ZiyiWang58/talking-plant-radio/hardware/images/01.jpg

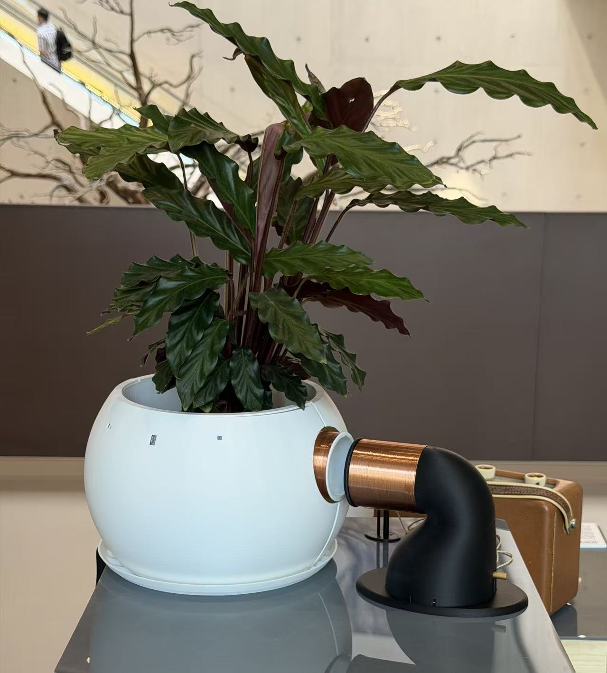
hardware/images/01.jpg
