ZiyiWang58/talking-plant-radio/hardware/images/02.jpg

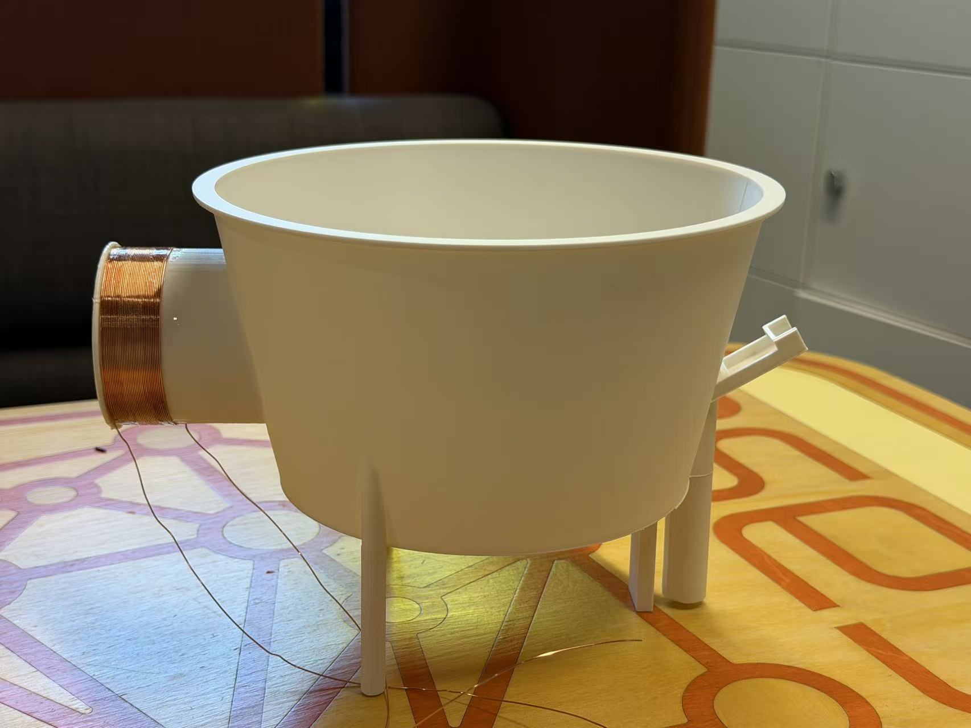
hardware/images/02.jpg
