ZiyiWang58/talking-plant-radio/hardware/images/03.jpg

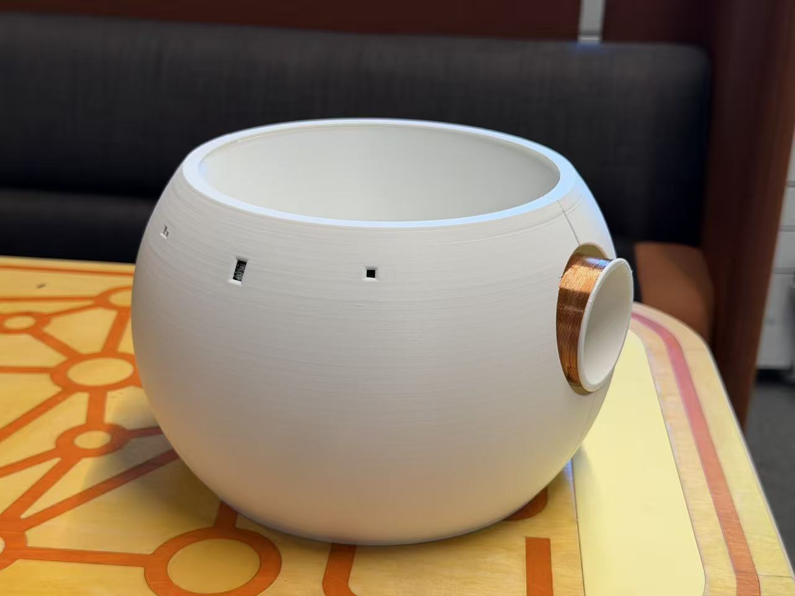
hardware/images/03.jpg
