ZiyiWang58/talking-plant-radio/hardware/images/04.jpg

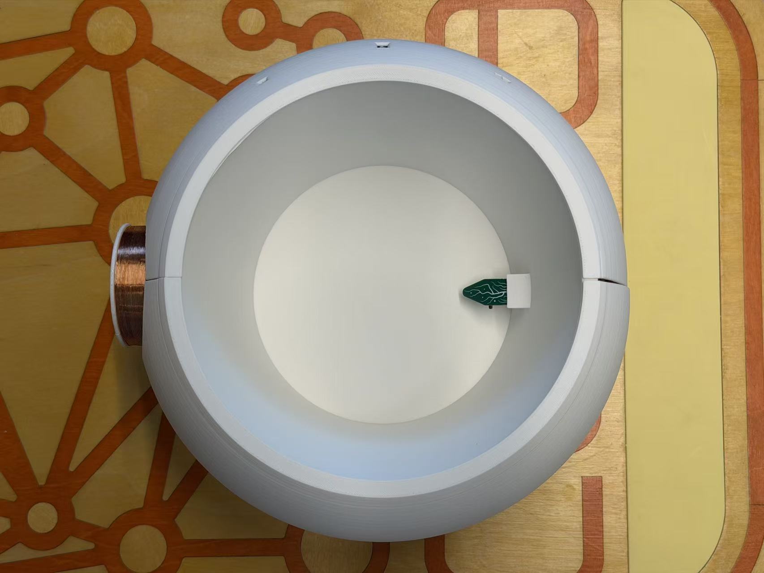
hardware/images/04.jpg
