ZiyiWang58/talking-plant-radio/hardware/images/figure2.jpg

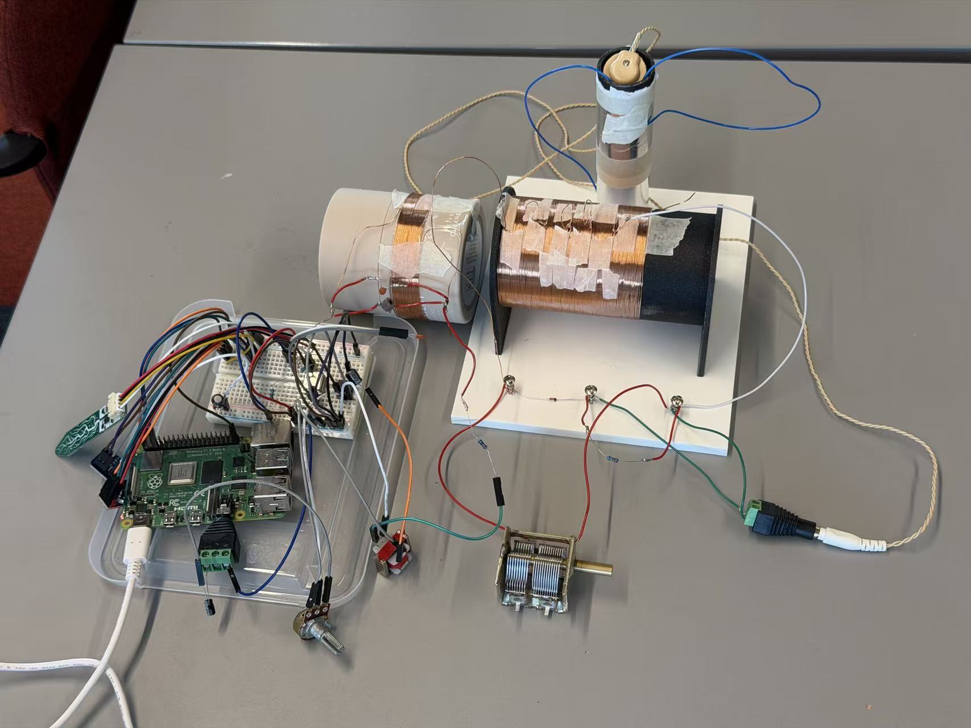
hardware/images/figure2.jpg
