ZiyiWang58/talking-plant-radio/hardware/images/PCB1.jpg

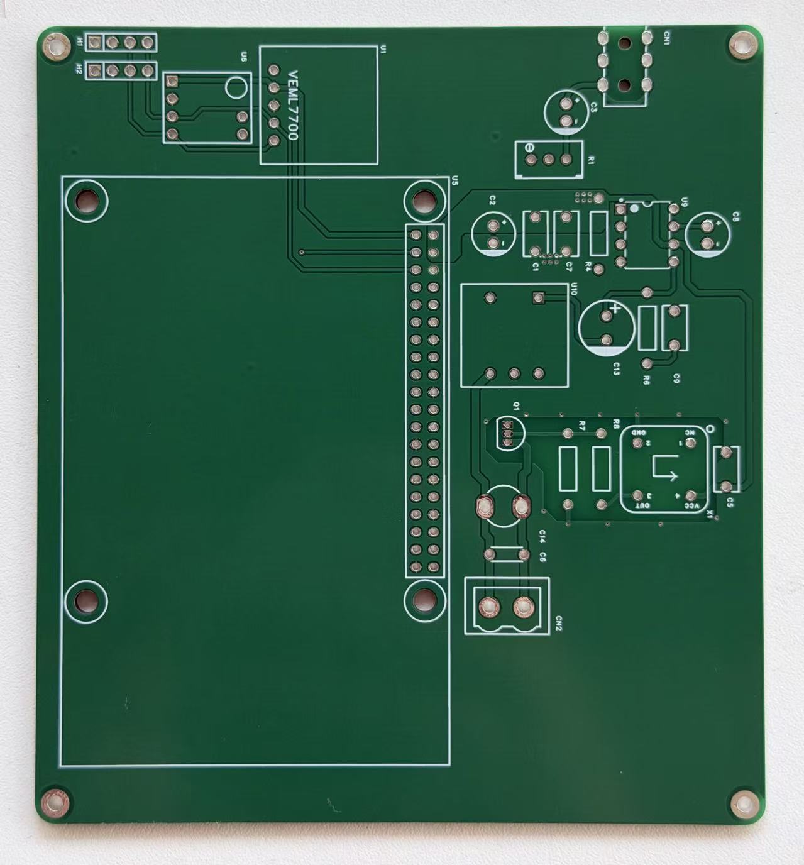
hardware/images/PCB1.jpg
