ZiyiWang58/talking-plant-radio/hardware/images/PCB2.jpg

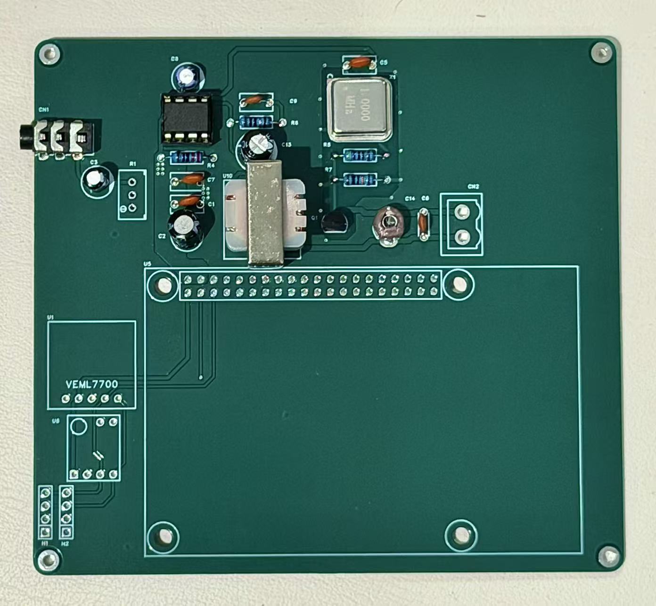
hardware/images/PCB2.jpg
