ZiyiWang58/talking-plant-radio/hardware/images/radio1.png

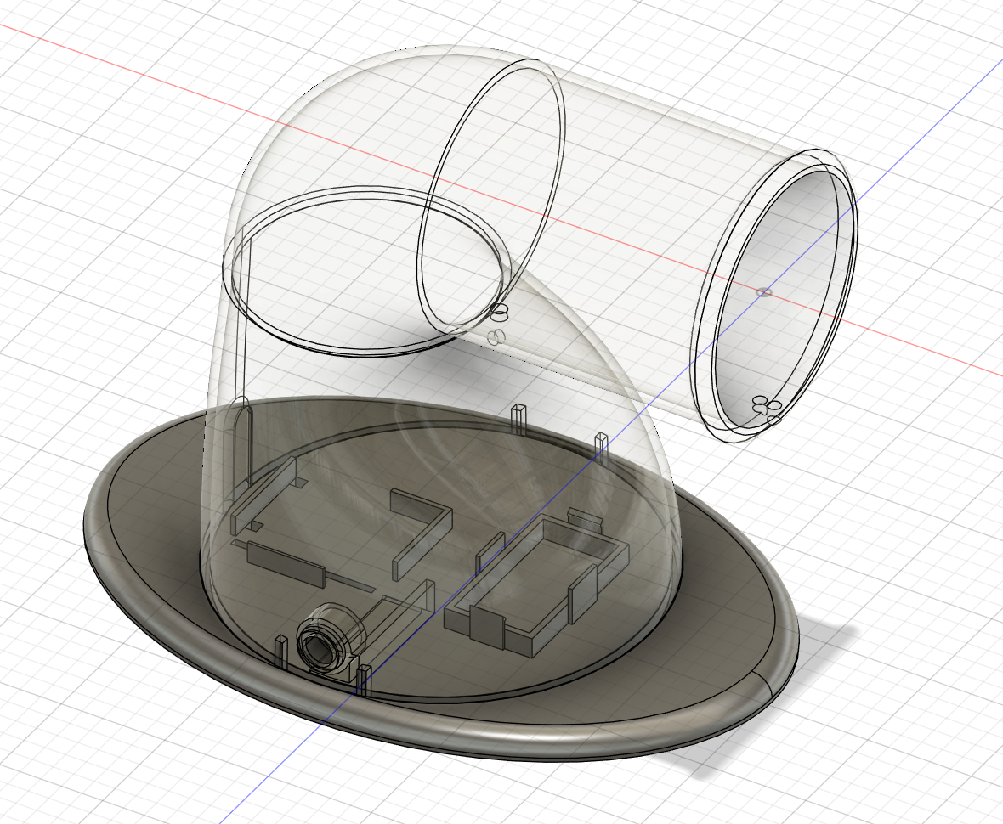
hardware/images/radio1.png
