ZiyiWang58/talking-plant-radio/hardware/images/radio2.jpg

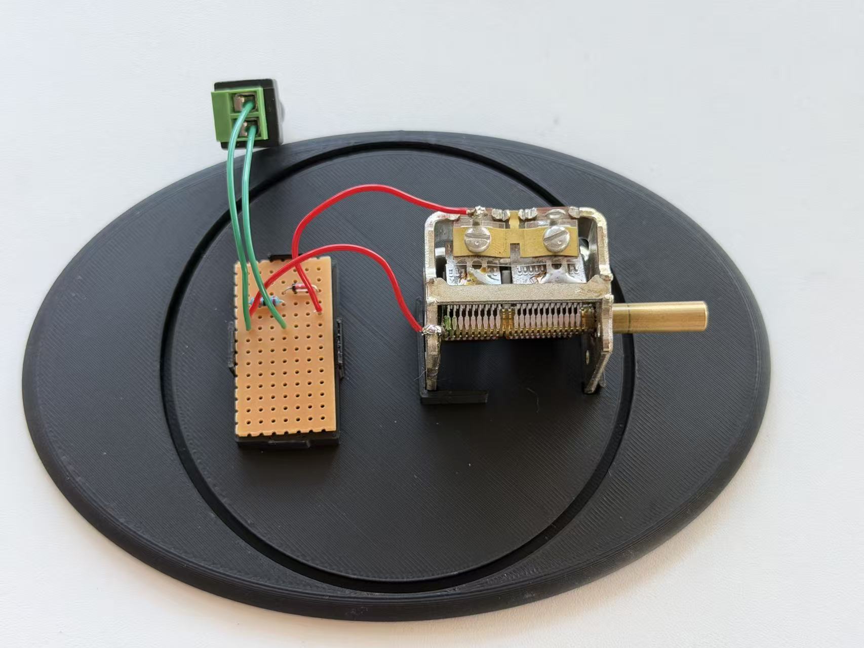
hardware/images/radio2.jpg
