ZiyiWang58/talking-plant-radio/hardware/images/radio.png

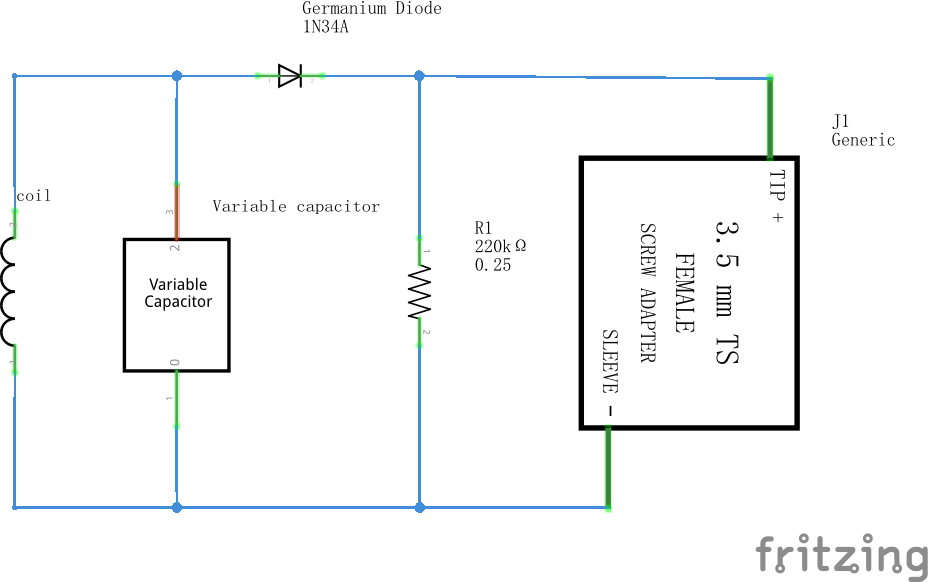
hardware/images/radio.png
