ZiyiWang58/talking-plant-radio/hardware/images/spectral.png

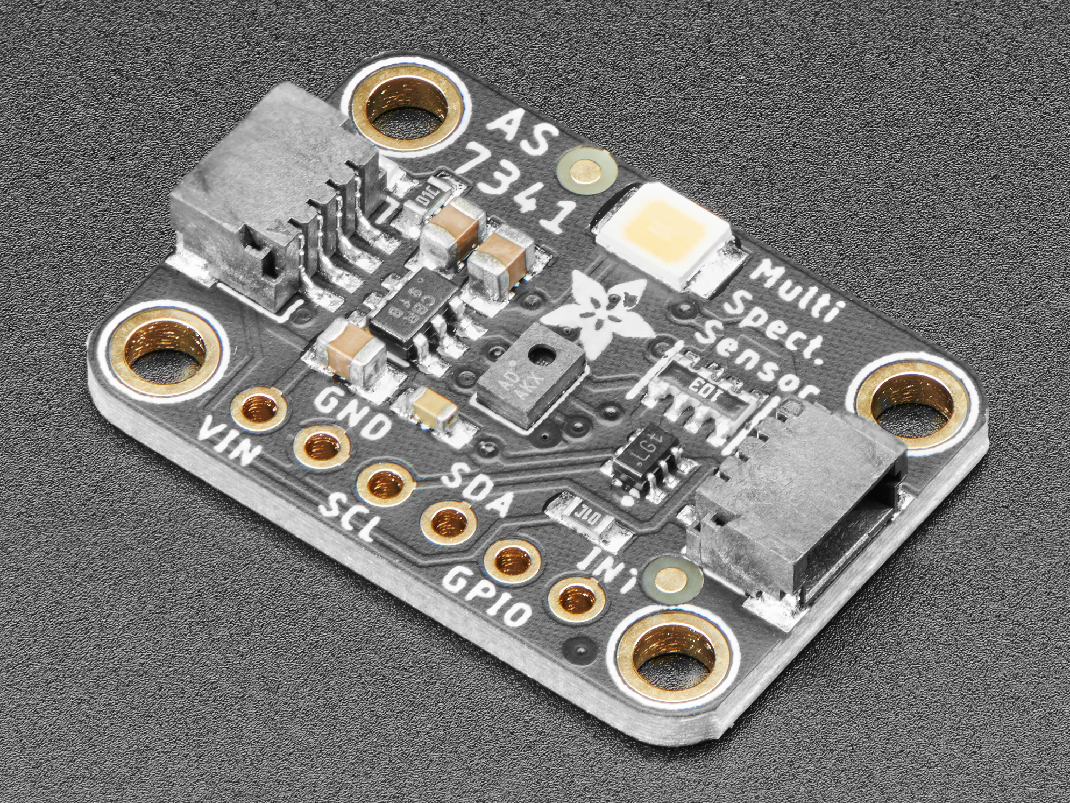
hardware/images/spectral.png
