ZiyiWang58/talking-plant-radio/hardware/images/temperature-humidity.jpg

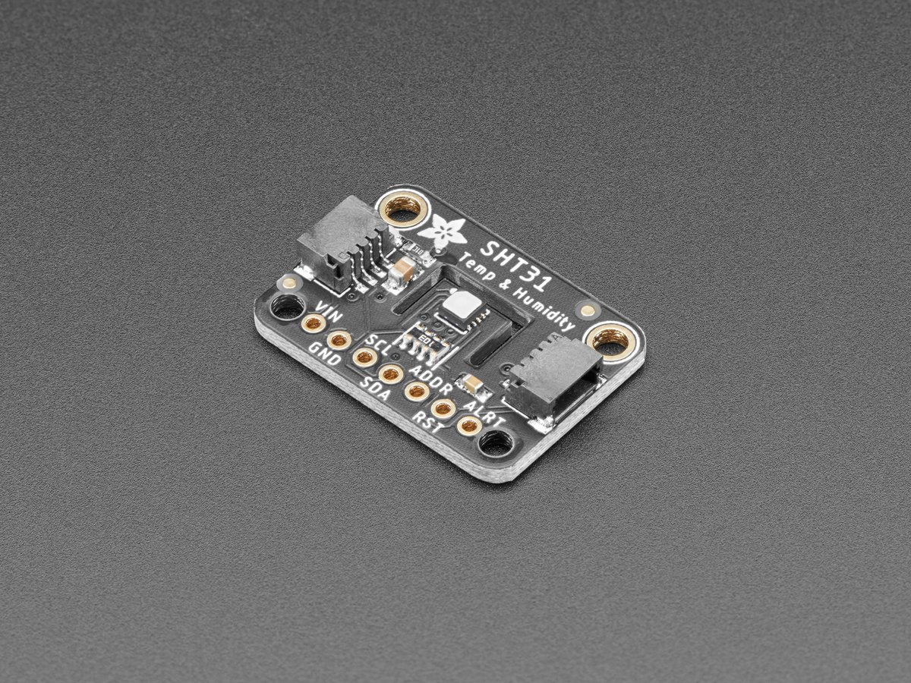
hardware/images/temperature-humidity.jpg
